miraclezero/HomeBrew/python/blinkenlights.py

#!/usr/bin/python

import time
import argparse

import board
import neopixel
# set led 
import RPi.GPIO as gpio
gpio.setmode(gpio.BCM)
ActiveLED = int(16) #pin 36
InactiveLED= int(19) #pin 35
gpio.setup(ActiveLED, gpio.OUT)
gpio.setup(InactiveLED, gpio.OUT)

pixels = neopixel.NeoPixel(board.D18, 12)

parser = argparse.ArgumentParser()
parser.add_argument('-reward_happened', type=bool, default=False)
args = parser.parse_args()
reward_happened = args.reward_happened
    

lights_on_hours = [21, 22, 23, 0, 1,  2, 3, 4, 5, 6, 7, 8]


def turn_light(on=True):
    for i in range(len(pixels)):
        if on:
            pixels[i] = (255, 255, 255)
        else:
            pixels[i] = (0, 0, 0)


def reward_cue_light():
    turn_light()
    gpio.output(ActiveLED, 0)
    time.sleep(0.5)
    turn_light(on=False)
    gpio.output(ActiveLED, 1)
    time.sleep(0.5)
    gpio.output(ActiveLED, 0)
    time.sleep(0.5)
    gpio.output(ActiveLED, 1)
    time.sleep(0.5)
    gpio.output(ActiveLED, 0)
    time.sleep(0.5)
    gpio.output(ActiveLED, 1)


if __name__ == "__main__":
    if reward_happened:
        reward_cue_light()    
    # if the current hour is in light on period, turn the light on
    if time.localtime().tm_hour in lights_on_hours:
        turn_light()
    else:
        turn_light(on=False)
